criterionsignalworks/mashiro/testing/tek0014.csv

Model | MDO4104C
Firmware Version | 1.06
Waveform Type | RF_FD
Point Format | Y
Horizontal Units | Hz
Horizontal Scale | 2e+07
Sample Interval | 200000
Record Length | 1001
Gating | 0.099900099900% to 100.0%
Probe Attenuation | 1
Vertical Units | dBm
Vertical Offset | 0
Vertical Scale | 10
Vertical Position | 0
Center Frequency | 5.7e+09
Span | 2e+08
Reference Level | 20
Label
FREQUENCY | FD NORM
5.6000000000e+09 | -55.0286
5.6002000000e+09 | -50.4992
5.6004000000e+09 | -48.0584
5.6006000000e+09 | -46.9051
5.6008000000e+09 | -46.5803
5.6010000000e+09 | -46.7655
5.6012000000e+09 | -47.2583
5.6014000000e+09 | -48.0126
5.6016000000e+09 | -49.1555
5.6018000000e+09 | -50.9591
5.6020000000e+09 | -53.8355
5.6022000000e+09 | -58.3706
5.6024000000e+09 | -63.2751
5.6026000000e+09 | -60.5299
5.6028000000e+09 | -57.0247
5.6030000000e+09 | -55.0675
5.6032000000e+09 | -54.1959
5.6034000000e+09 | -54.2472
5.6036000000e+09 | -55.2412
5.6038000000e+09 | -57.1884
5.6040000000e+09 | -59.7046
5.6042000000e+09 | -61.3018
5.6044000000e+09 | -61.0223
5.6046000000e+09 | -60.3096
5.6048000000e+09 | -60.0117
5.6050000000e+09 | -60.0686
5.6052000000e+09 | -60.3713
5.6054000000e+09 | -61.0836
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
