criterionsignalworks/mashiro/testing/tim.csv

!CSV A.01.01
!Agilent Technologies | E8364C | MY43040503 | A.09.42.15
!Agilent E8364C: A.09.42.15
!Date: Friday | March 12 | 2021 15:24:26
!Source: Standard
BEGIN CH1_DATA
Freq(Hz) | S11(DB) | S11(DEG) | S21(DB) | S21(DEG)
10000000 | -18.783176 | -65.717796 | -14.203536 | 64.256035
59950000 | -11.939095 | 168.17477 | 5.9377551 | 143.47942
109900000 | -17.733238 | 59.979301 | -13.059225 | -15.102324
159850000 | -16.810637 | -90.530586 | -11.21968 | -65.736443
209800000 | -14.069181 | 133.76245 | -5.6415577 | 153.36806
259750000 | -13.628235 | -15.56511 | -2.7179425 | 1.7801366
309700000 | -11.693063 | -164.21469 | -0.64038086 | -150.78947
359650000 | -11.271498 | 48.590576 | 0.87748957 | 57.886559
409600000 | -10.176359 | -104.72395 | 1.9579921 | -96.095421
459550000 | -9.425416 | 108.81667 | 2.9561779 | 111.54745
509500000 | -9.153038 | -45.664795 | 3.7232814 | -43.247799
559450000 | -8.2255878 | 166.17616 | 4.5811977 | 165.31825
609400000 | -8.2769794 | 13.351979 | 5.1411076 | 12.154936
659350000 | -7.4851394 | -138.75883 | 5.6525726 | -140.599
709300000 | -7.2531362 | 71.363129 | 6.1123395 | 66.981934
759250000 | -6.5252547 | -82.818977 | 6.7563319 | -86.685432
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
